Makerfabs/ESP32-S3-Parallel-TFT-with-Touch-4inch/example/fs_test/data/img3.jpg

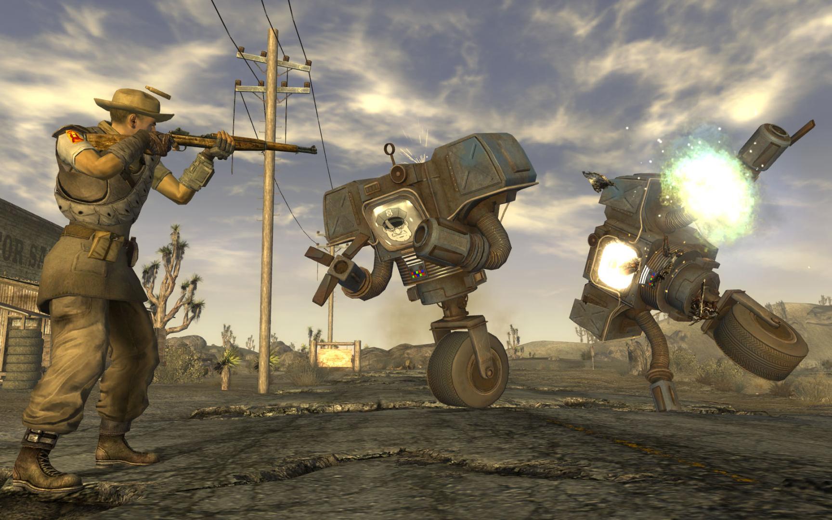
example/fs_test/data/img3.jpg
