Makerfabs/ESP32-S3-Parallel-TFT-with-Touch-4inch/kit/src/kit/color.h

//the colors we will be using
const uint16_t camColors[] = {
    0x480F,
    0x400F,
    0x400F,
    0x400F,
    0x4010,
    0x3810,
    0x3810,
    0x3810,
    0x3810,
    0x3010,
    0x3010,
    0x3010,
    0x2810,
    0x2810,
    0x2810,
    0x2810,
    0x2010,
    0x2010,
    0x2010,
    0x1810,
    0x1810,
    0x1811,
    0x1811,
    0x1011,
    0x1011,
    0x1011,
    0x0811,
    0x0811,
    0x0811,
    0x0011,
    0x0011,
    0x0011,
    0x0011,
    0x0011,
    0x0031,
    0x0031,
    0x0051,
    0x0072,
    0x0072,
    0x0092,
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
};
